fm4dd/gm-proto-e1/fabfiles-smd/images/20220923-gm-proto-e1-kicad.png.png

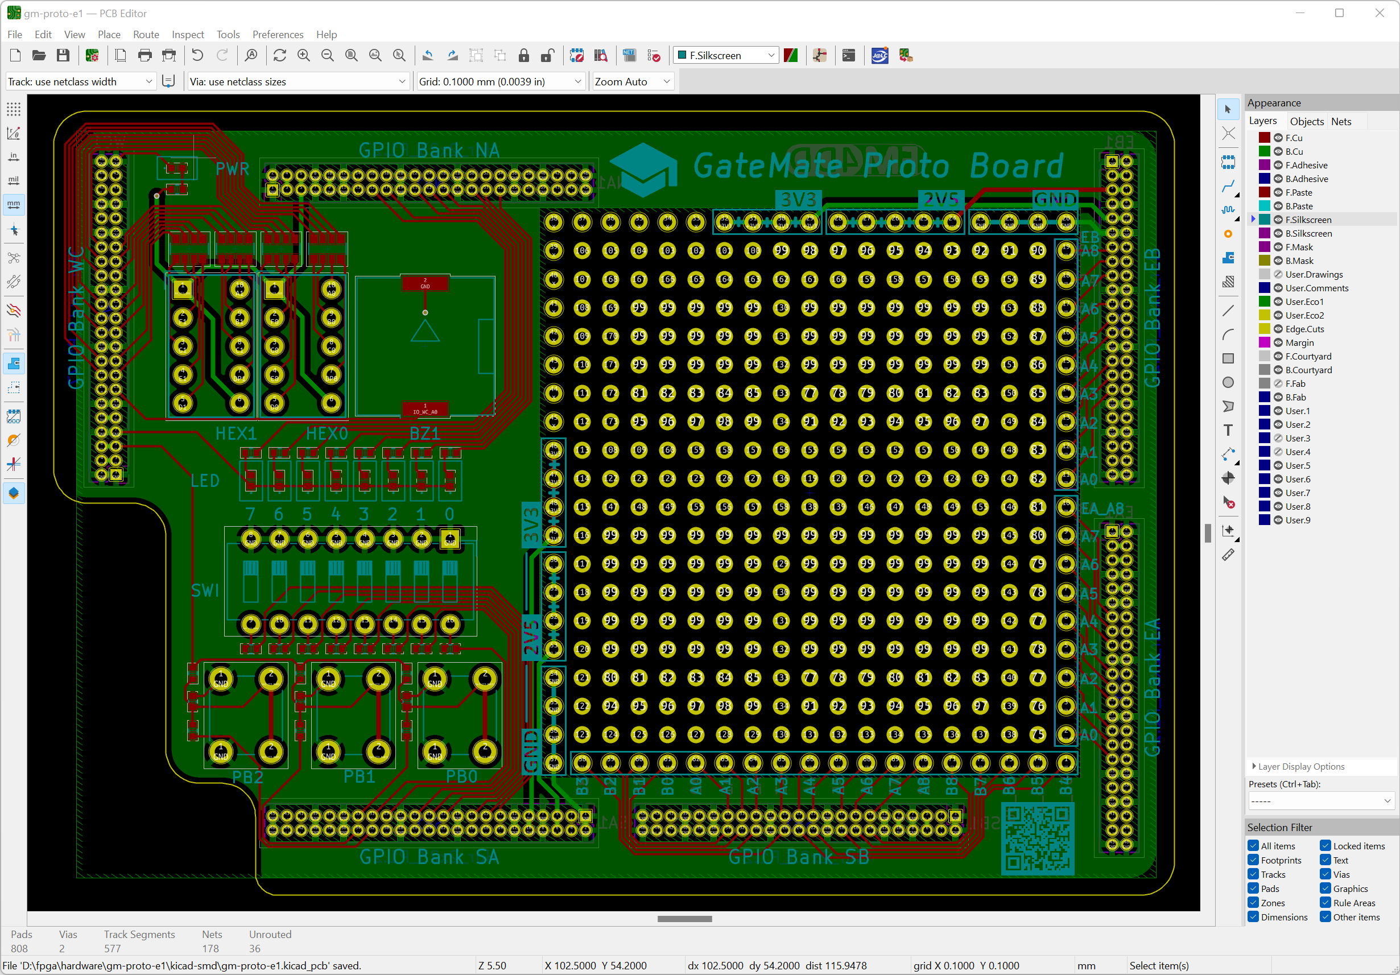
fabfiles-smd/images/20220923-gm-proto-e1-kicad.png.png
